openUC2/UC2_Fluorescence_microscope/IMAGES/Application_Fluorescence_Microscope_Infinity_cellstorm_v3.png

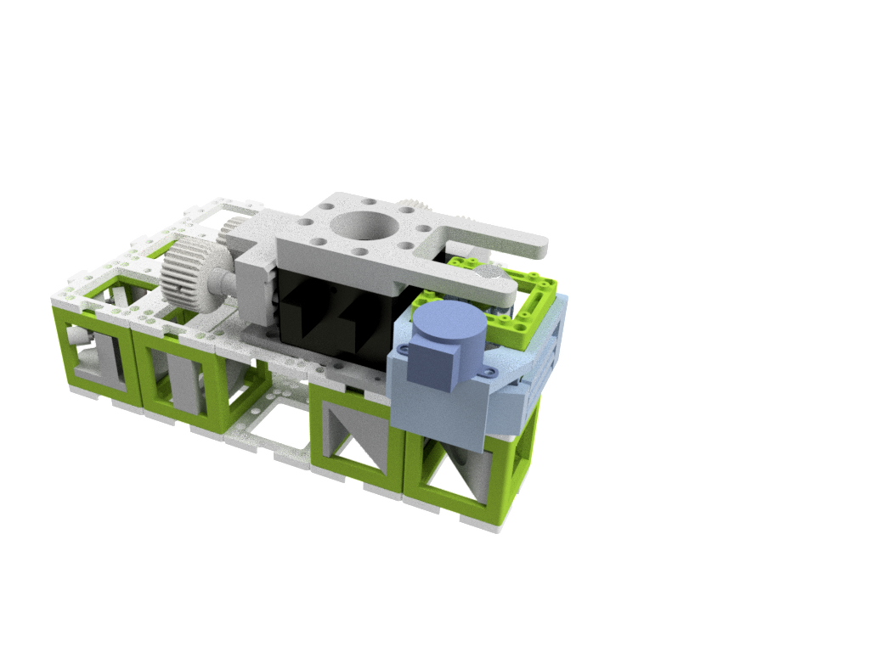
IMAGES/Application_Fluorescence_Microscope_Infinity_cellstorm_v3.png
