openUC2/UC2_Fluorescence_microscope/IMAGES/IMG_20211126_092207.jpg

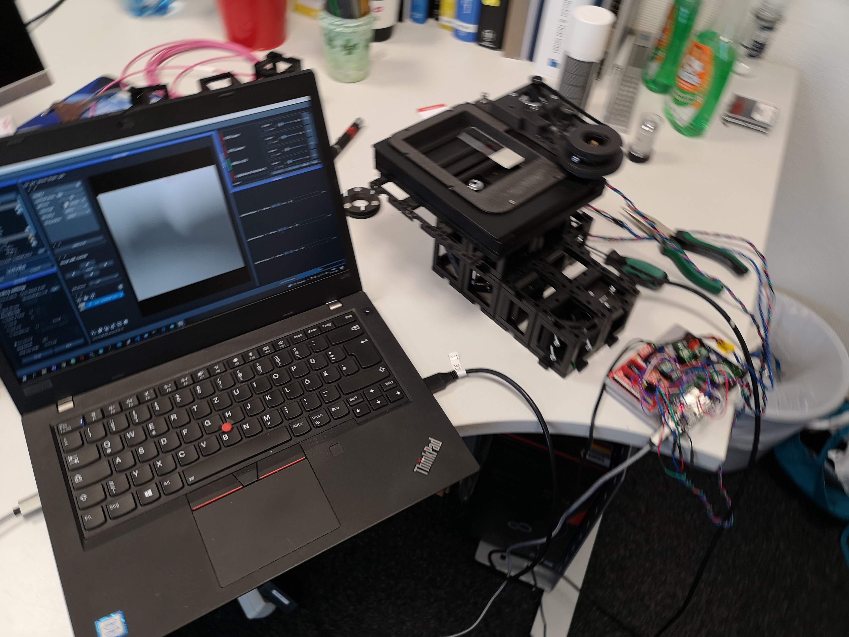
IMAGES/IMG_20211126_092207.jpg
