openUC2/UC2_Fluorescence_microscope/STL/APP_UC2_STORM__30_cellSTORM_UC2_Laser_base_38.stl

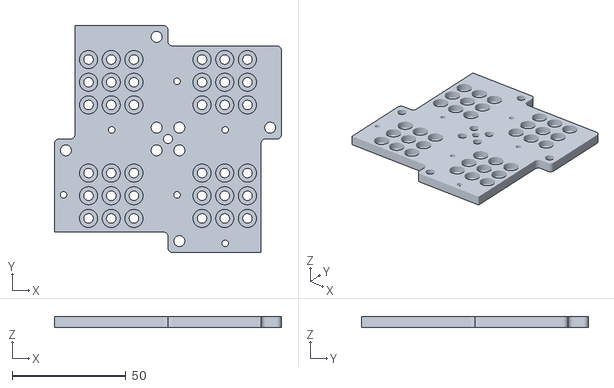
[picture p27: CAD file, 2021-11-30]
STL/APP_UC2_STORM__30_cellSTORM_UC2_Laser_base_38.stl
100.0 x 100.0 x 5.00
