openUC2/UC2_Fluorescence_microscope/STL/APP_UC2_STORM__30_cellSTORM_UC2_motorized_xystage_spacer_39.stl

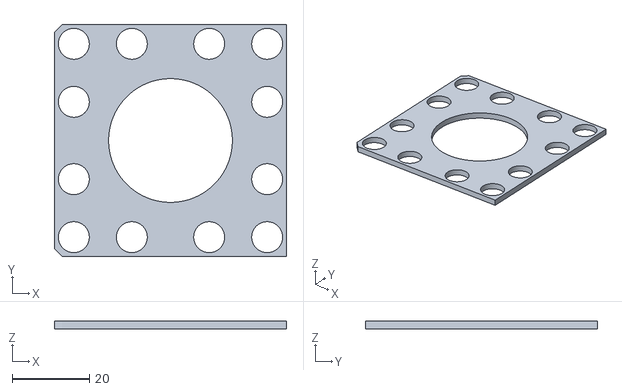
[picture p28: CAD file, 2021-11-30]
STL/APP_UC2_STORM__30_cellSTORM_UC2_motorized_xystage_spacer_39.stl
60.0 x 60.0 x 2.00
