openUC2/UC2_Fluorescence_microscope/STL/APP_UC2_STORM__30_Cube_Z_Focus_MGN_NEMA_base_v3_104.stl

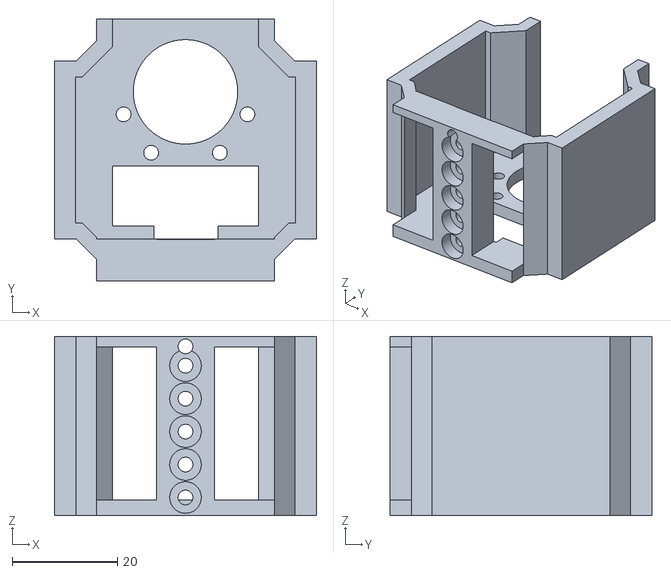
[picture p29: CAD file, 2021-11-30]
STL/APP_UC2_STORM__30_Cube_Z_Focus_MGN_NEMA_base_v3_104.stl
49.7 x 49.7 x 34.0
