openUC2/UC2_Fluorescence_microscope/STL/APP_UC2_STORM__30_Cube_Z_Focus_MGN_NEMA_Motoradapter_NEMA11_v3_111.stl

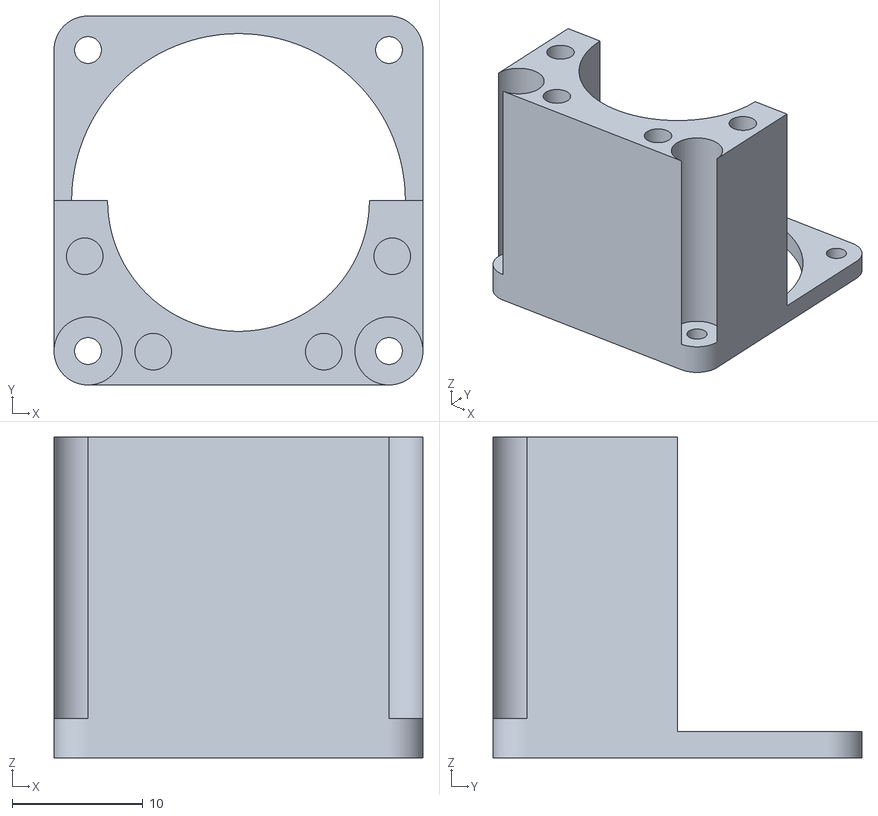
[picture p30: CAD file, 2021-11-30]
STL/APP_UC2_STORM__30_Cube_Z_Focus_MGN_NEMA_Motoradapter_NEMA11_v3_111.stl
28.2 x 28.2 x 24.5
