openUC2/UC2_Fluorescence_microscope/STL/APP_UC2_STORM__10_Base_puzzle_v3_126.stl

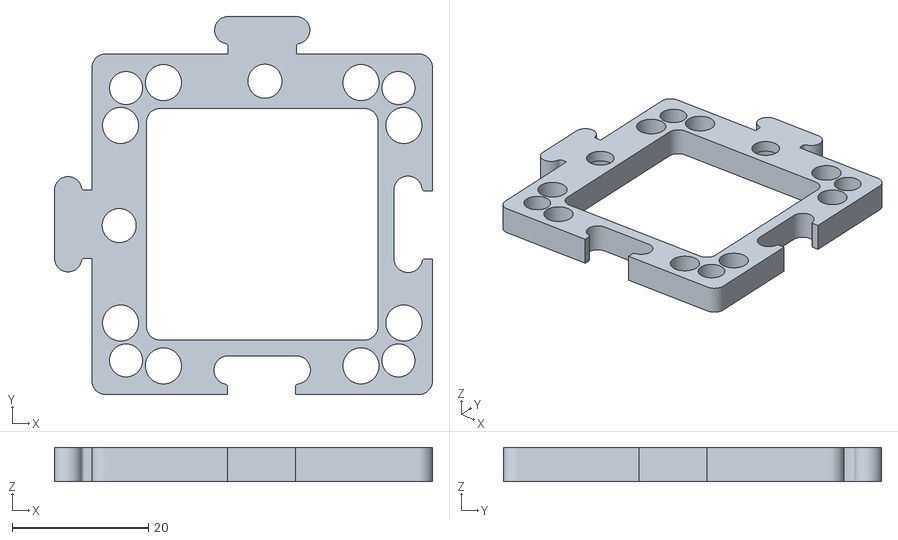
[picture p31: CAD file, 2021-11-30]
STL/APP_UC2_STORM__10_Base_puzzle_v3_126.stl
55.5 x 55.5 x 5.00
