openUC2/UC2_Fluorescence_microscope/STL/APP_UC2_STORM__20_Cube_Insert_Lens_165mm_clamp_16.stl

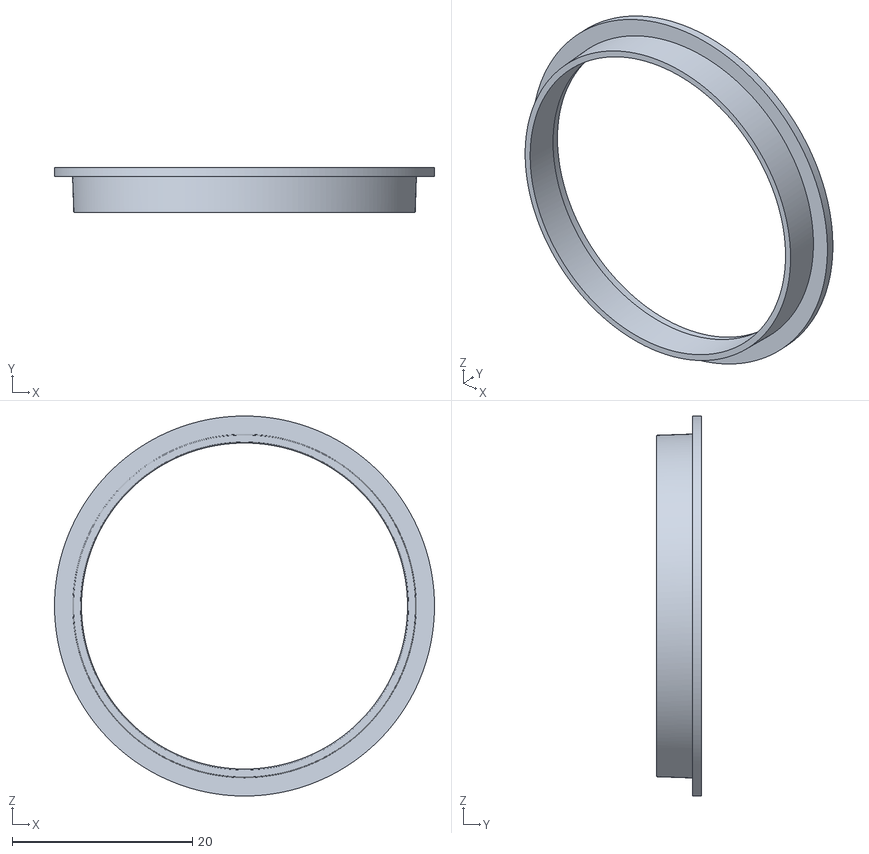
[picture p32: CAD file, 2021-11-30]
STL/APP_UC2_STORM__20_Cube_Insert_Lens_165mm_clamp_16.stl
42.2 x 5.00 x 42.2
