openUC2/UC2_Fluorescence_microscope/STL/APP_UC2_STORM__20_Cube_insert_AlliedVision_Alvium_v3_134.stl

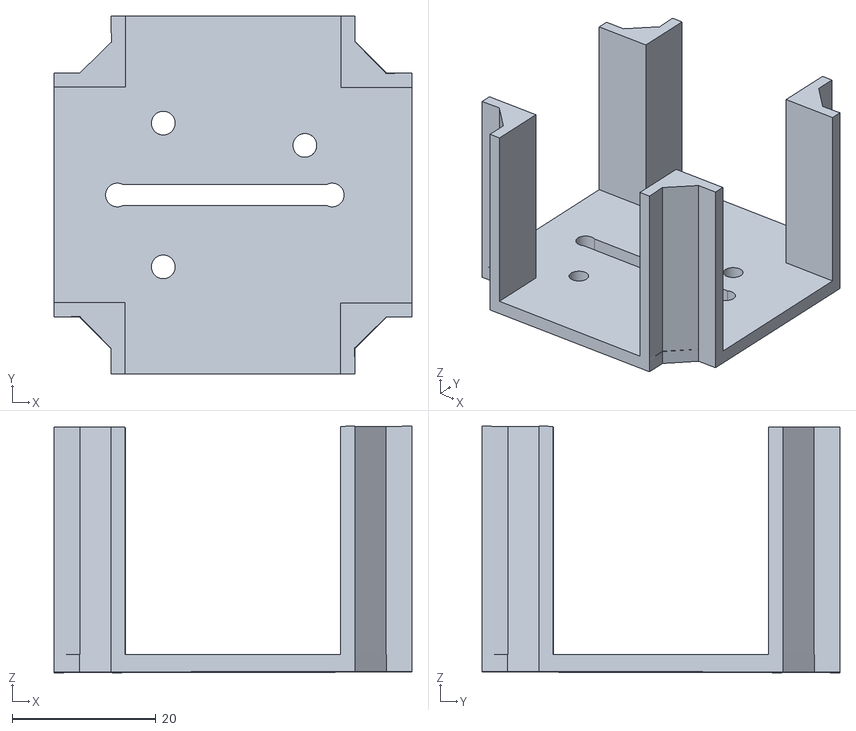
[picture p33: CAD file, 2021-11-30]
STL/APP_UC2_STORM__20_Cube_insert_AlliedVision_Alvium_v3_134.stl
49.8 x 49.8 x 34.3
