openUC2/UC2_Fluorescence_microscope/STL/APP_UC2_STORM__30_cellSTORM_UC2_motorized_micrometer_gear2_53.stl

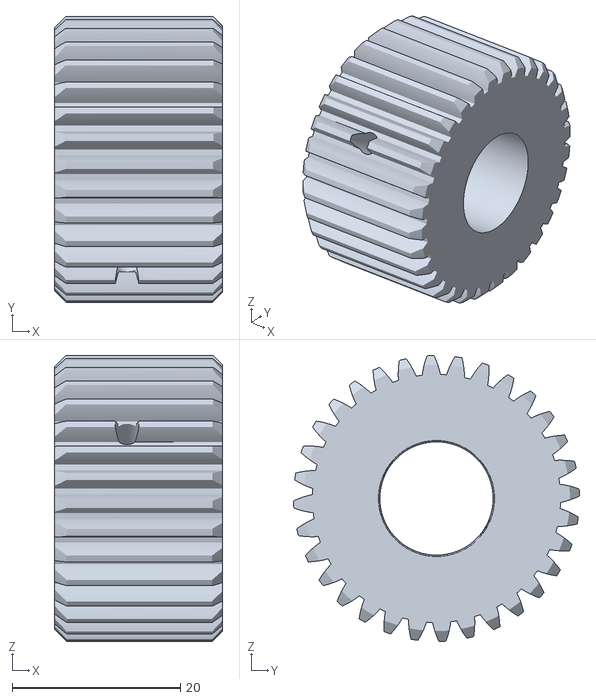
[picture p34: CAD file, 2021-11-30]
STL/APP_UC2_STORM__30_cellSTORM_UC2_motorized_micrometer_gear2_53.stl
20.0 x 34.0 x 34.0
