openUC2/UC2_Fluorescence_microscope/STL/APP_UC2_STORM__30_Mount_Nema_Motor_attachement_for_XYstage_v3_55.stl

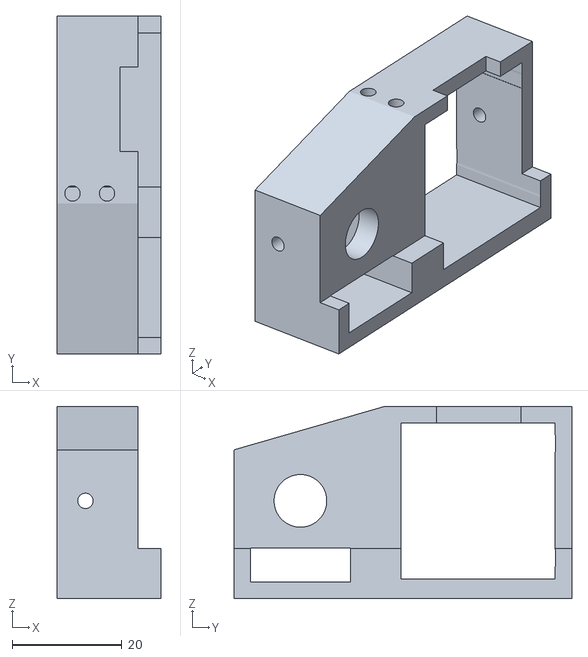
[picture p35: CAD file, 2021-11-30]
STL/APP_UC2_STORM__30_Mount_Nema_Motor_attachement_for_XYstage_v3_55.stl
19.0 x 61.6 x 35.0
