openUC2/UC2_Fluorescence_microscope/STL/APP_UC2_STORM__20_Cube_Insert_Lens_165mm_7.stl

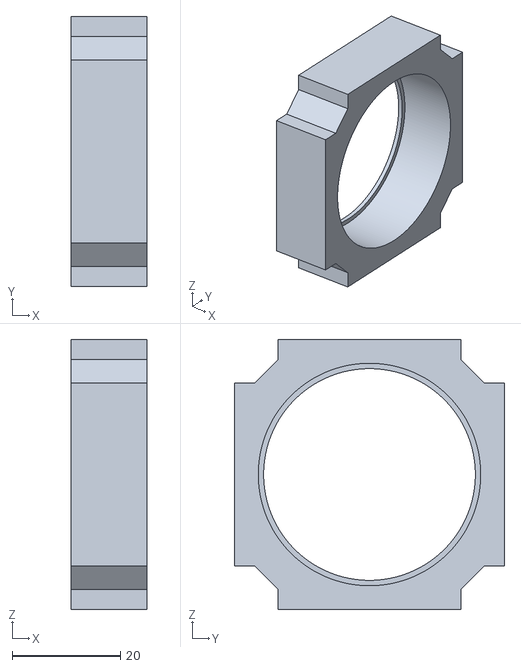
[picture p37: CAD file, 2021-11-30]
STL/APP_UC2_STORM__20_Cube_Insert_Lens_165mm_7.stl
14.0 x 50.0 x 50.0
