openUC2/UC2_Fluorescence_microscope/STL/APP_UC2_STORM__20_Cube_Insert_Beamsplittercube_Dichroicmirror_Retainplate_25_36_85.stl

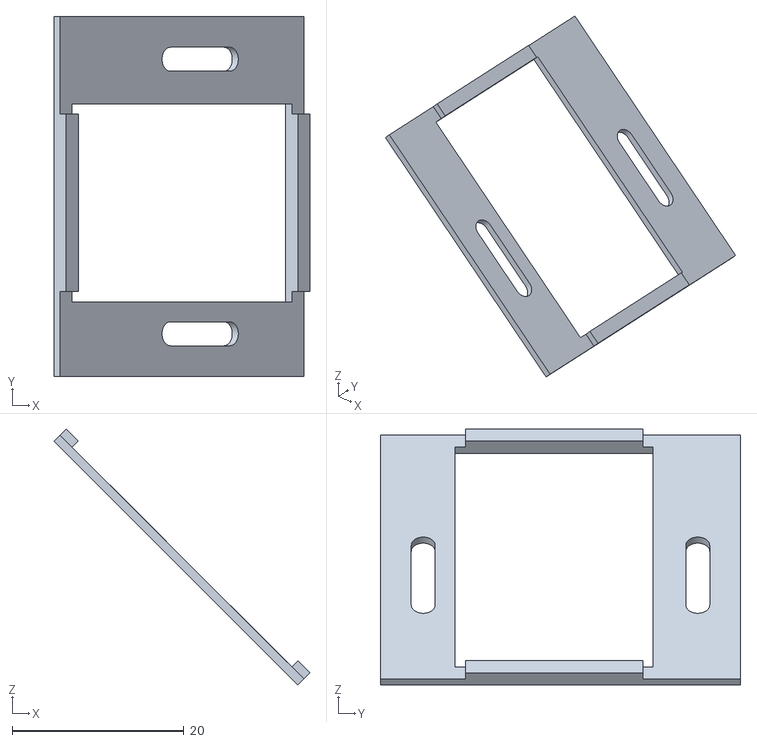
[picture p38: CAD file, 2021-11-30]
STL/APP_UC2_STORM__20_Cube_Insert_Beamsplittercube_Dichroicmirror_Retainplate_25_36_85.stl
29.8 x 42.0 x 29.8
