openUC2/UC2_Fluorescence_microscope/STL/APP_UC2_STORM__30_Cube_Z_Focus_MGN_NEMA_adapter_RMS_107.stl

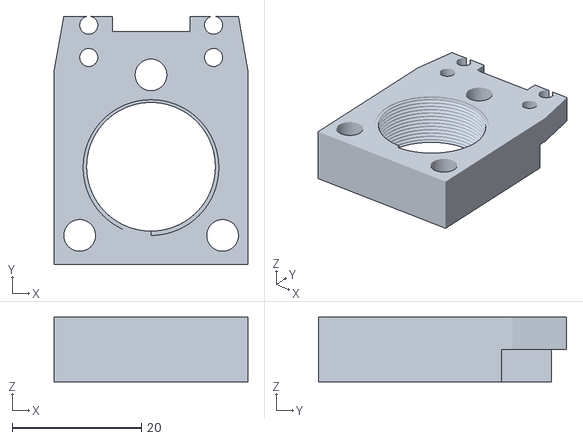
[picture p39: CAD file, 2021-11-30]
STL/APP_UC2_STORM__30_Cube_Z_Focus_MGN_NEMA_adapter_RMS_107.stl
30.0 x 38.4 x 10.0
