openUC2/UC2_Fluorescence_microscope/STL/APP_UC2_STORM__20_Cube_insert_Laser_Block_adjustable_v3_136.stl

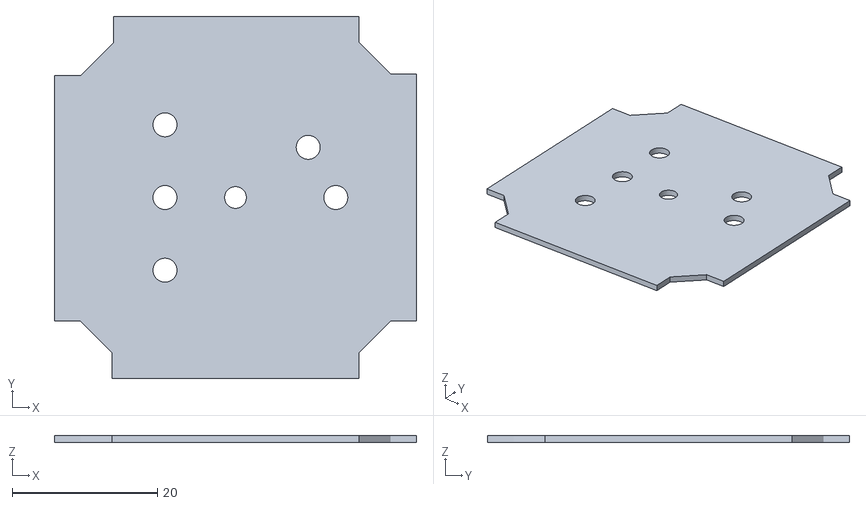
[picture p40: CAD file, 2021-11-30]
STL/APP_UC2_STORM__20_Cube_insert_Laser_Block_adjustable_v3_136.stl
49.8 x 49.8 x 1.00
