openUC2/UC2_Fluorescence_microscope/STL/APP_UC2_STORM__30_cellSTORM_UC2_Sample_arm_ptycho_40.stl

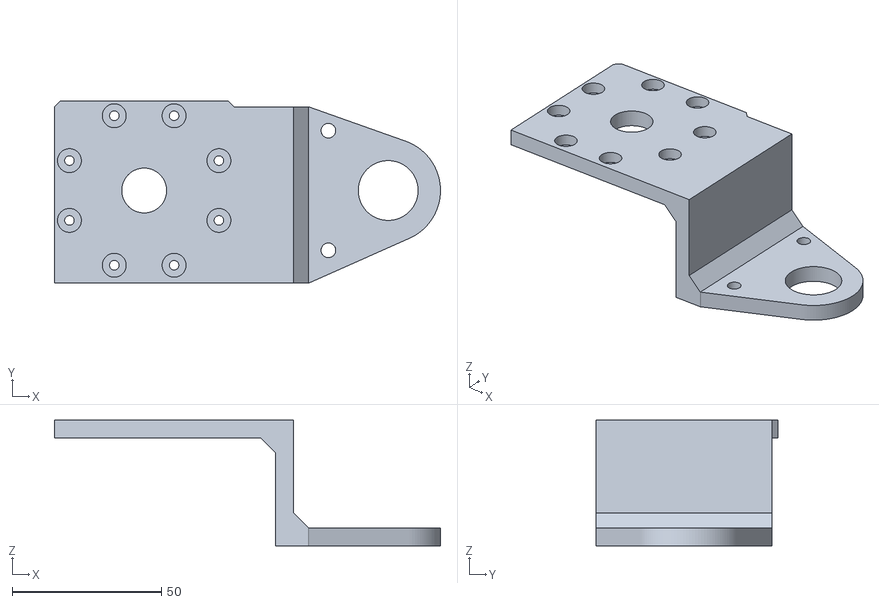
[picture p41: CAD file, 2021-11-30]
STL/APP_UC2_STORM__30_cellSTORM_UC2_Sample_arm_ptycho_40.stl
129.1 x 61.0 x 42.0
