openUC2/UC2_Fluorescence_microscope/STL/APP_UC2_STORM__30_XY_Sample_arm_v3_37.stl

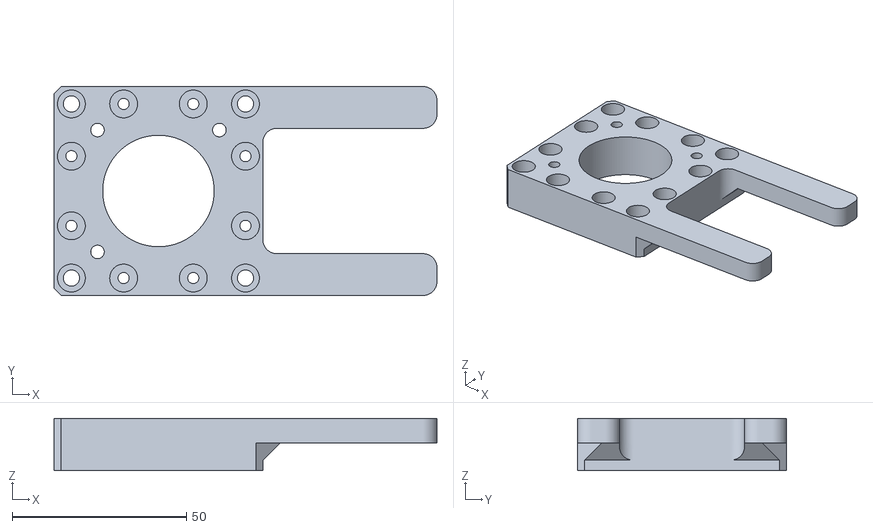
[picture p42: CAD file, 2021-11-30]
STL/APP_UC2_STORM__30_XY_Sample_arm_v3_37.stl
110.0 x 60.0 x 15.0
