openUC2/UC2_Fluorescence_microscope/STL/APP_UC2_STORM__30_cellSTORM_XY_Sample_arm_90degRot_v3_48.stl

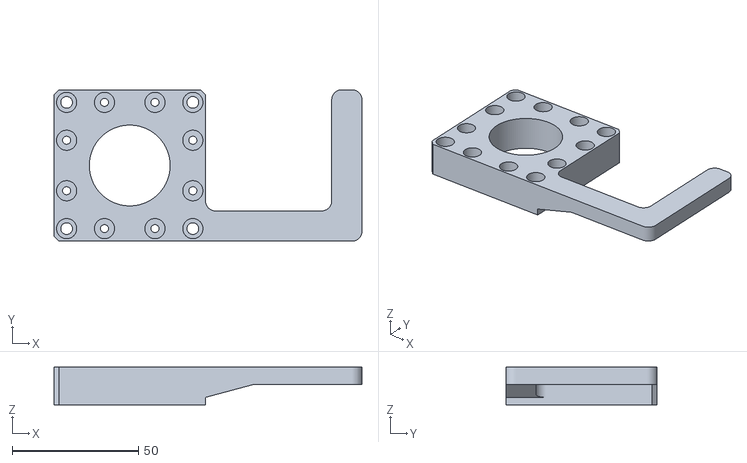
[picture p43: CAD file, 2021-11-30]
STL/APP_UC2_STORM__30_cellSTORM_XY_Sample_arm_90degRot_v3_48.stl
122.0 x 60.0 x 15.0
