openUC2/UC2_Fluorescence_microscope/STL/APP_UC2_STORM__30_Cube_Z_Focus_MGN_NEMA_Motorsupport_113.stl

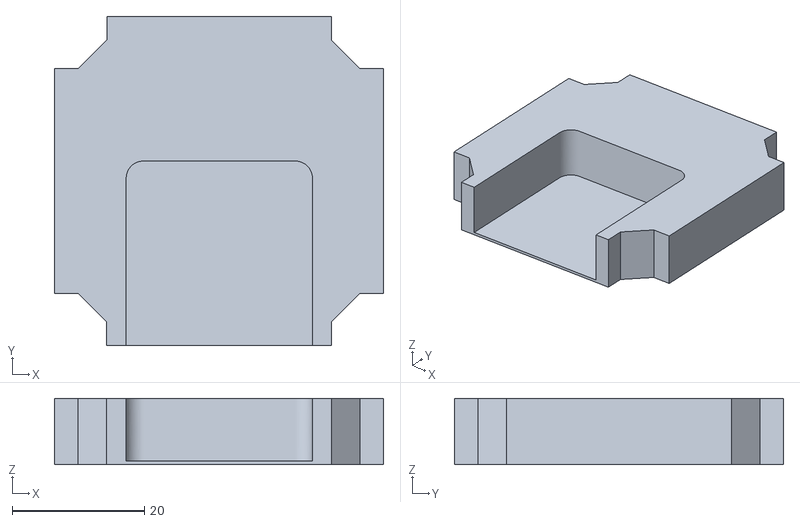
[picture p44: CAD file, 2021-11-30]
STL/APP_UC2_STORM__30_Cube_Z_Focus_MGN_NEMA_Motorsupport_113.stl
49.8 x 49.8 x 10.0
