openUC2/UC2_Fluorescence_microscope/STL/APP_UC2_STORM__30_Cube_Z_Focus_Drylin_NEMA_slide_part1_110.stl

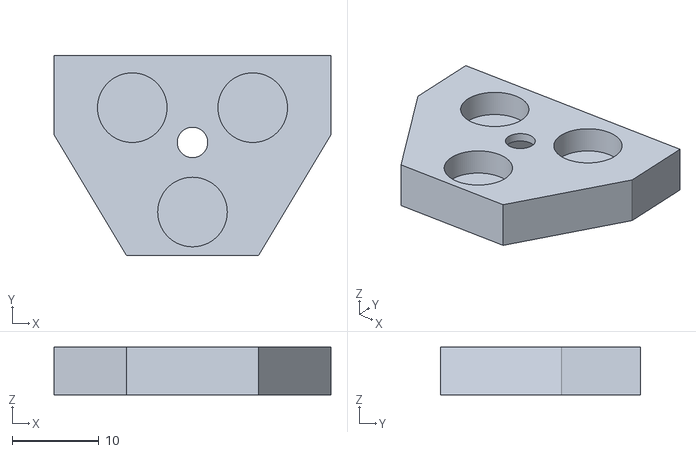
[picture p45: CAD file, 2021-11-30]
STL/APP_UC2_STORM__30_Cube_Z_Focus_Drylin_NEMA_slide_part1_110.stl
31.9 x 23.0 x 5.50
