openUC2/UC2_Fluorescence_microscope/STL/APP_UC2_STORM__30_Cube_Z_Focus_MGN_NEMA_Motoradapter_28BYJ_v3_112.stl

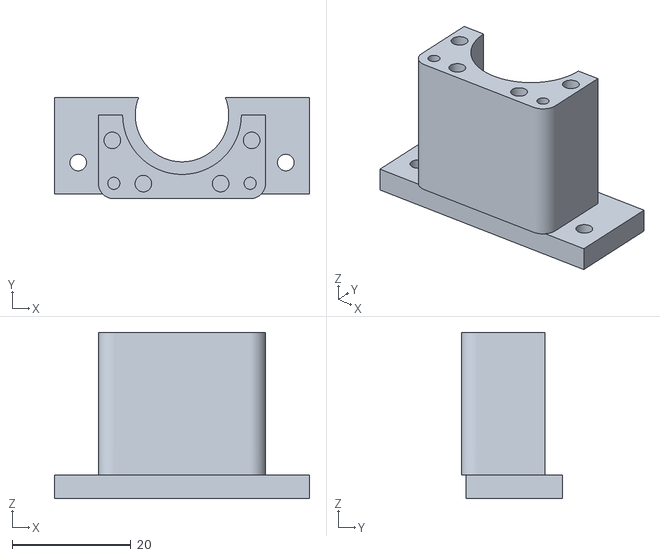
[picture p46: CAD file, 2021-11-30]
STL/APP_UC2_STORM__30_Cube_Z_Focus_MGN_NEMA_Motoradapter_28BYJ_v3_112.stl
43.0 x 17.1 x 28.0
